JLNapo/BorneGEMI/Documents/Liste Composants.jpg

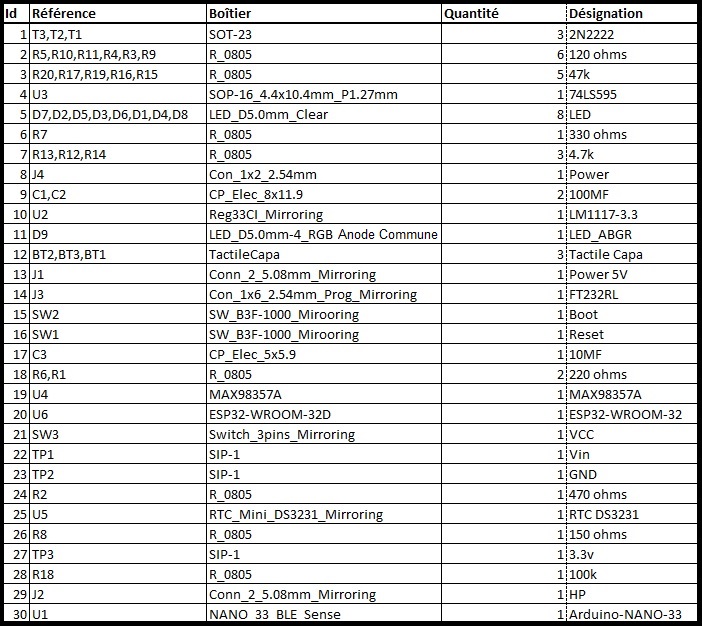
Documents/Liste Composants.jpg
