JLNapo/BorneGEMI/Documents/Plan Circuit.jpg

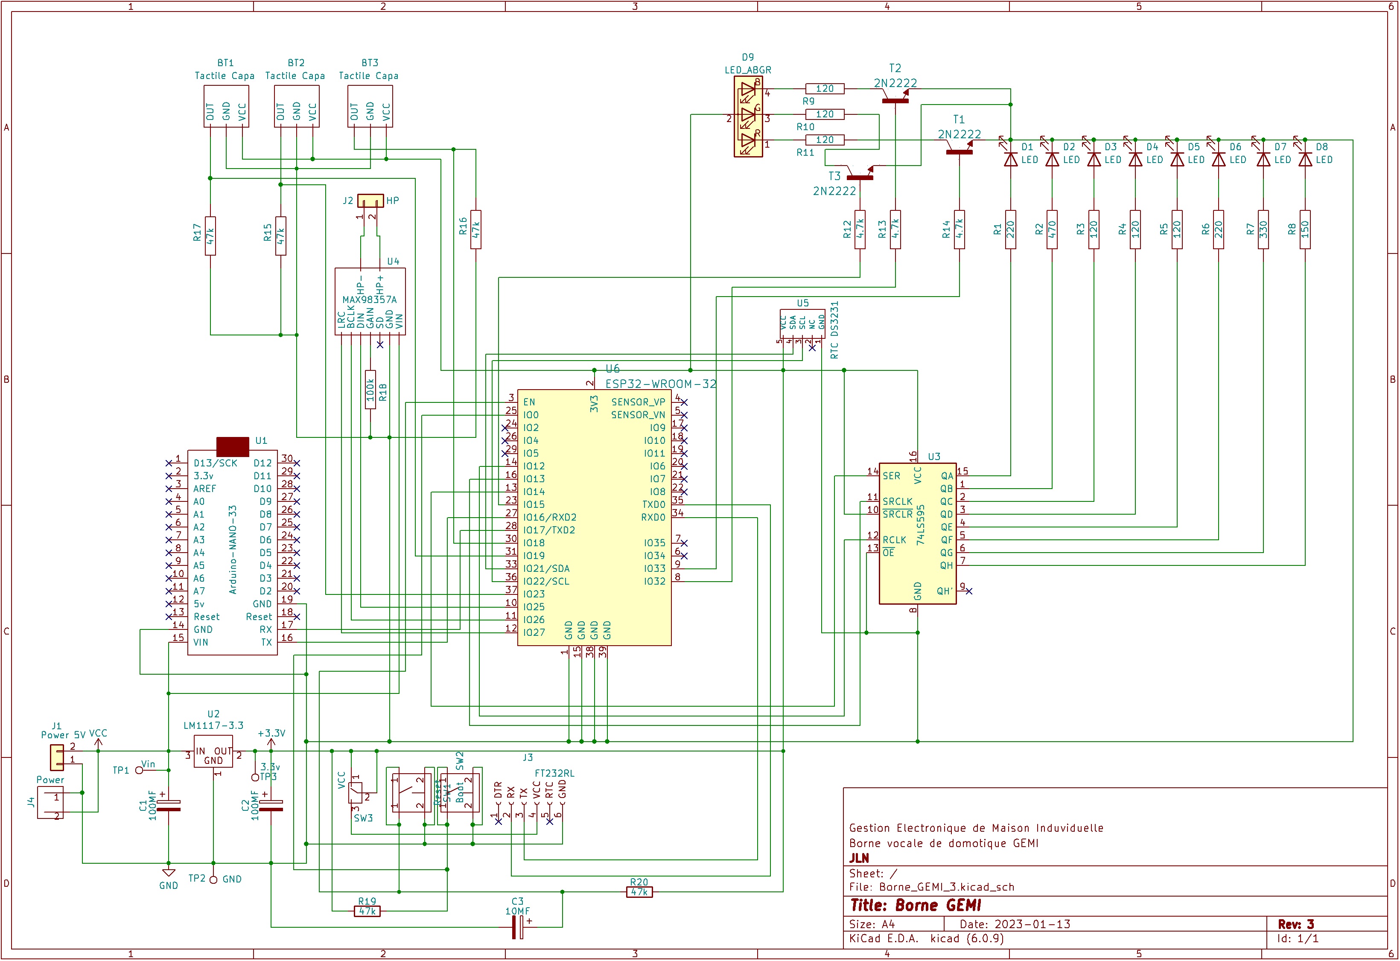
Documents/Plan Circuit.jpg
