JLNapo/BorneGEMI/Images/2N2222A_SMD.jpg

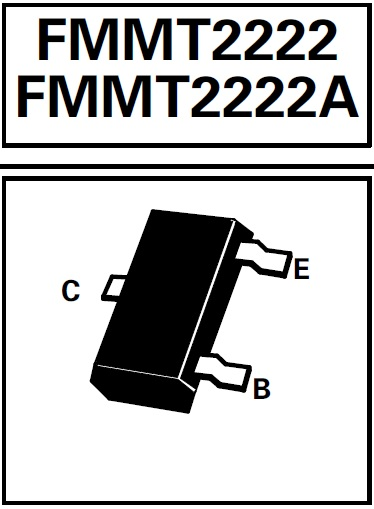
Images/2N2222A_SMD.jpg
