JLNapo/BorneGEMI/Images/74HC595-02.png

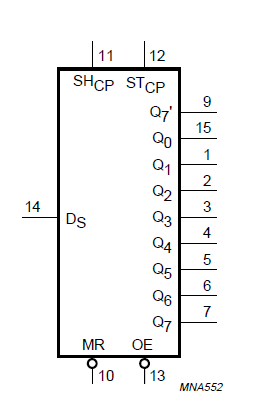
Images/74HC595-02.png
