JLNapo/BorneGEMI/Images/Alim-Diamètres.png

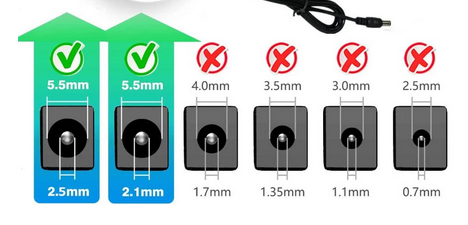
Images/Alim-Diamètres.png
