JLNapo/BorneGEMI/Images/BorneDessus.png

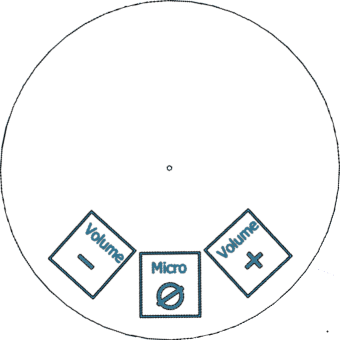
Images/BorneDessus.png
