JLNapo/BorneGEMI/Images/BorneDessusDouble.png

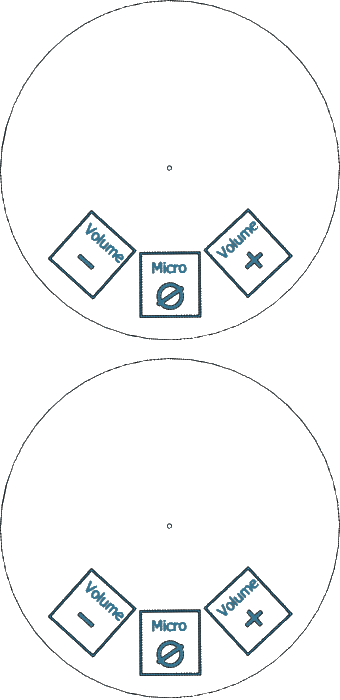
Images/BorneDessusDouble.png
