JLNapo/BorneGEMI/Images/Circuit Imprimé.jpg

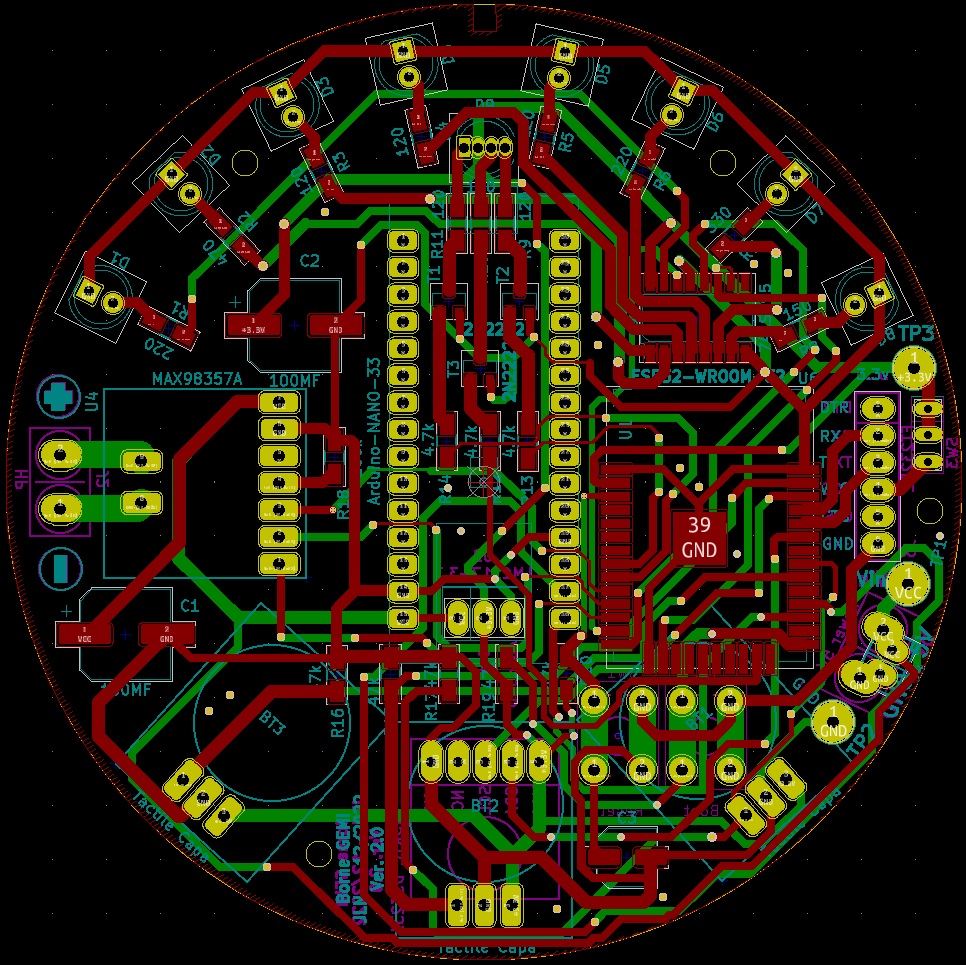
Images/Circuit Imprimé.jpg
