JLNapo/BorneGEMI/Images/DS3231.jpg

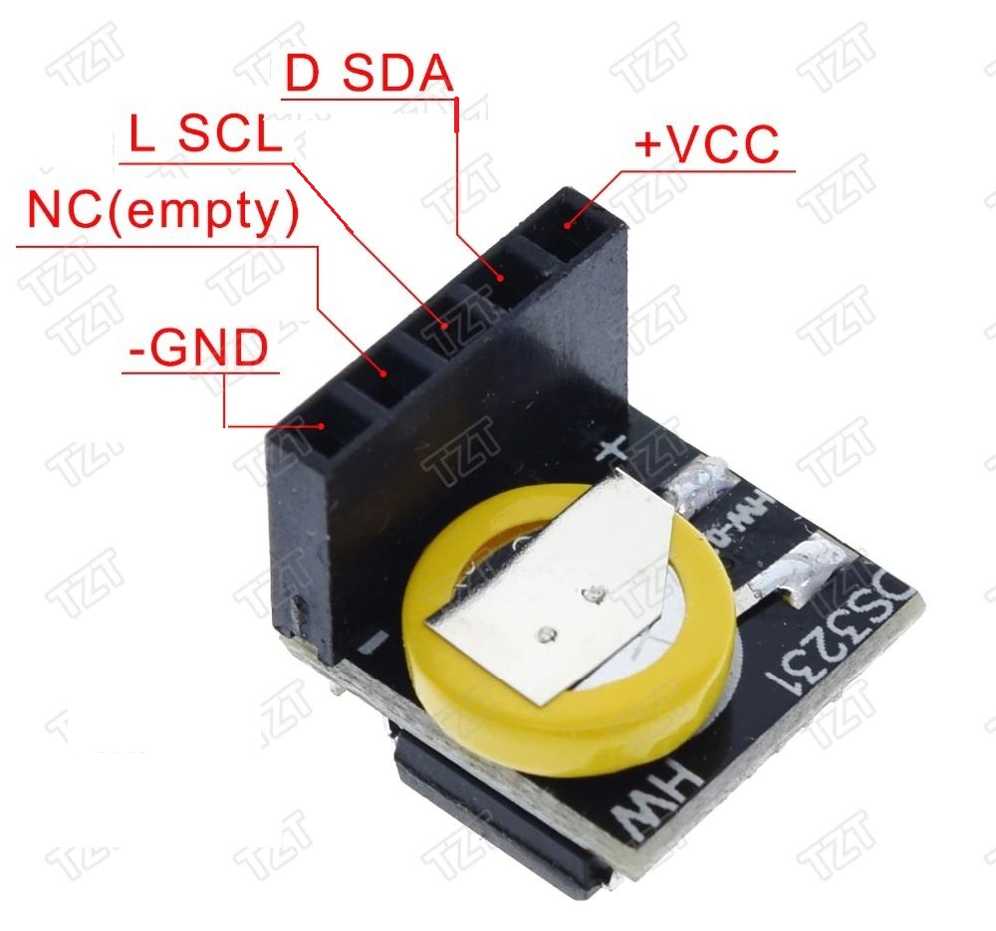
Images/DS3231.jpg
