JLNapo/BorneGEMI/Images/HTTM Dimensions.png

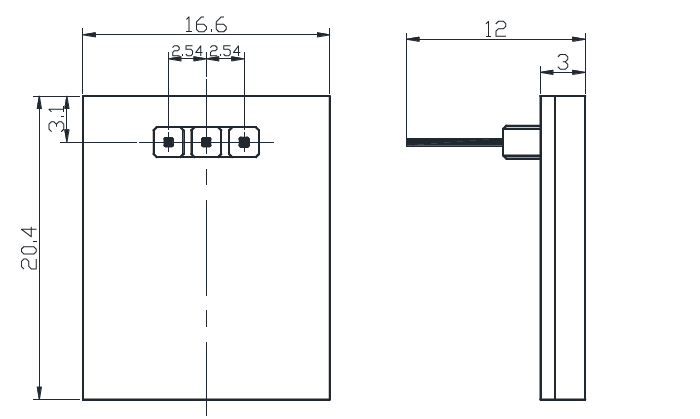
Images/HTTM Dimensions.png
