JLNapo/BorneGEMI/Images/img01.jpg

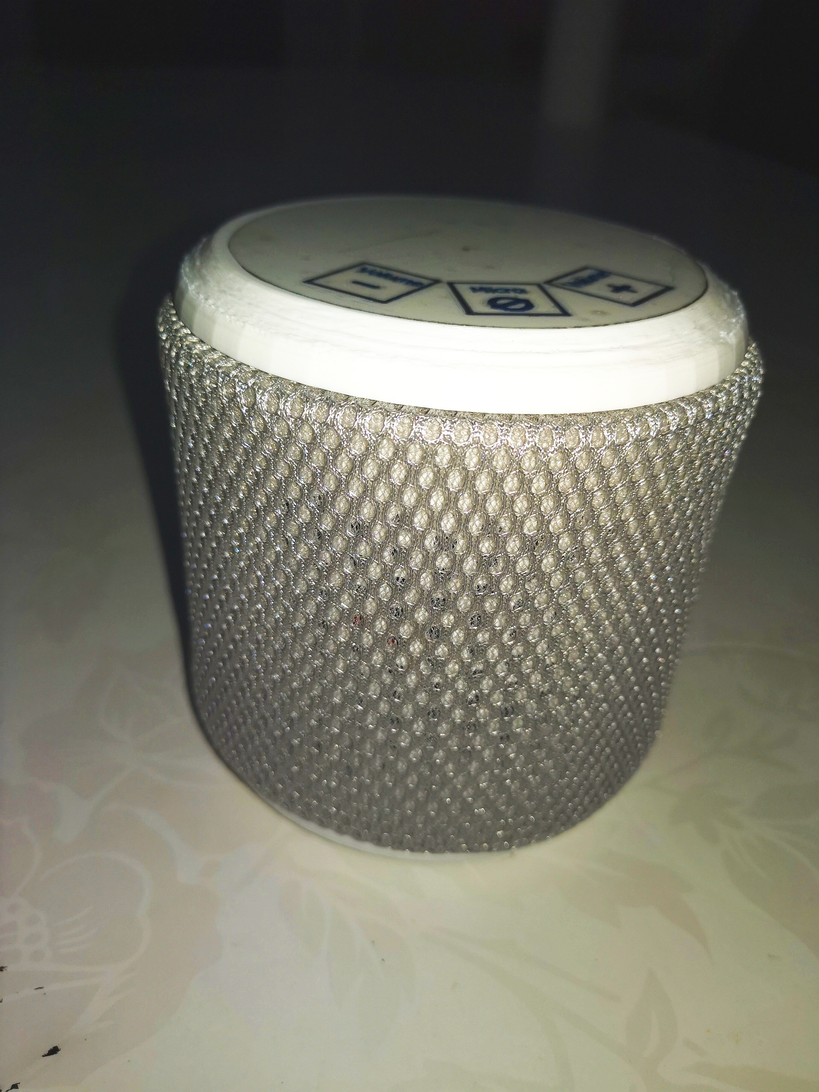
Images/img01.jpg
