JLNapo/BorneGEMI/Images/img02.jpg

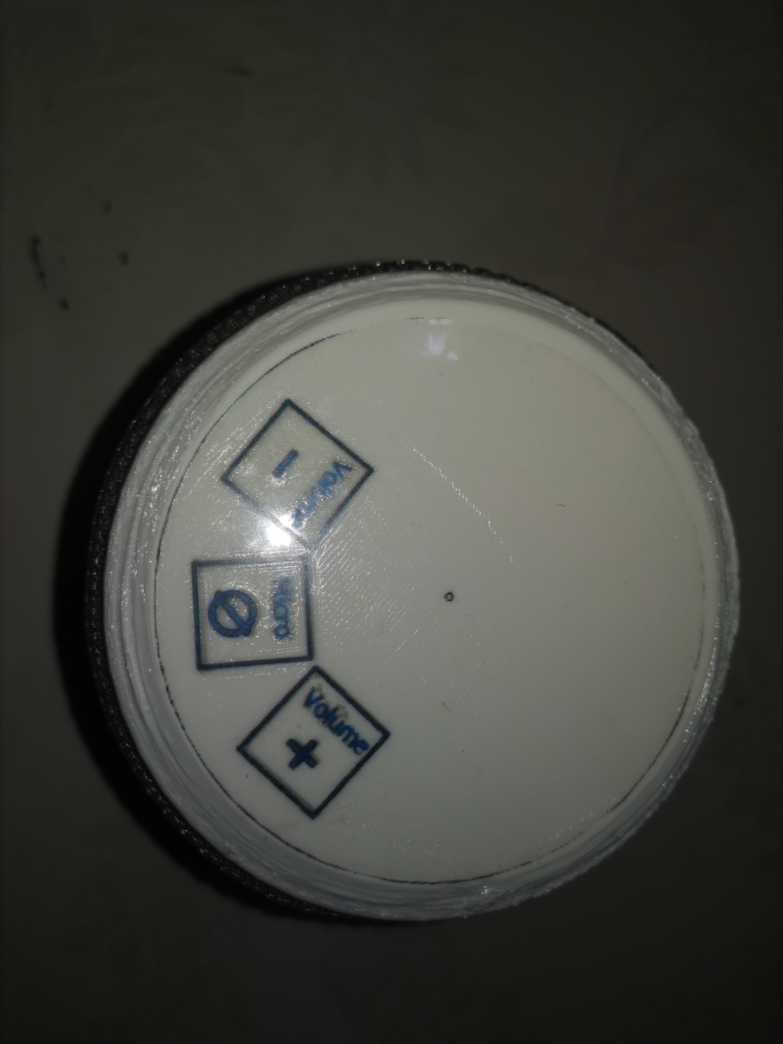
Images/img02.jpg
