JLNapo/BorneGEMI/Images/img03.jpg

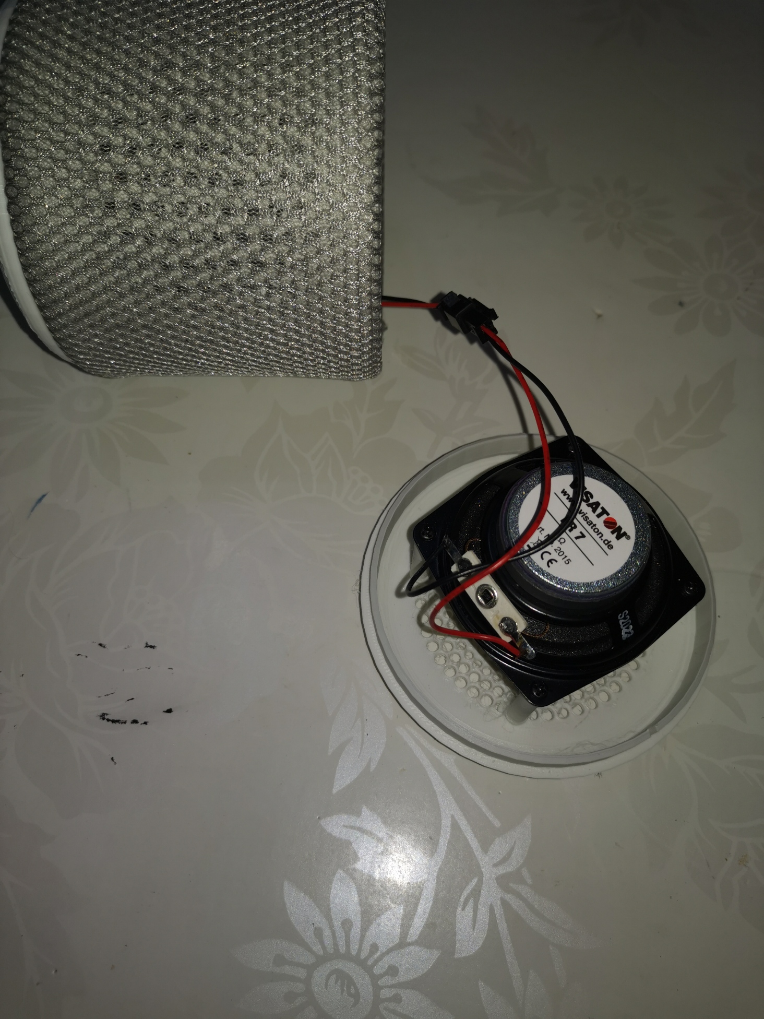
Images/img03.jpg
