JLNapo/BorneGEMI/Images/img04.jpg

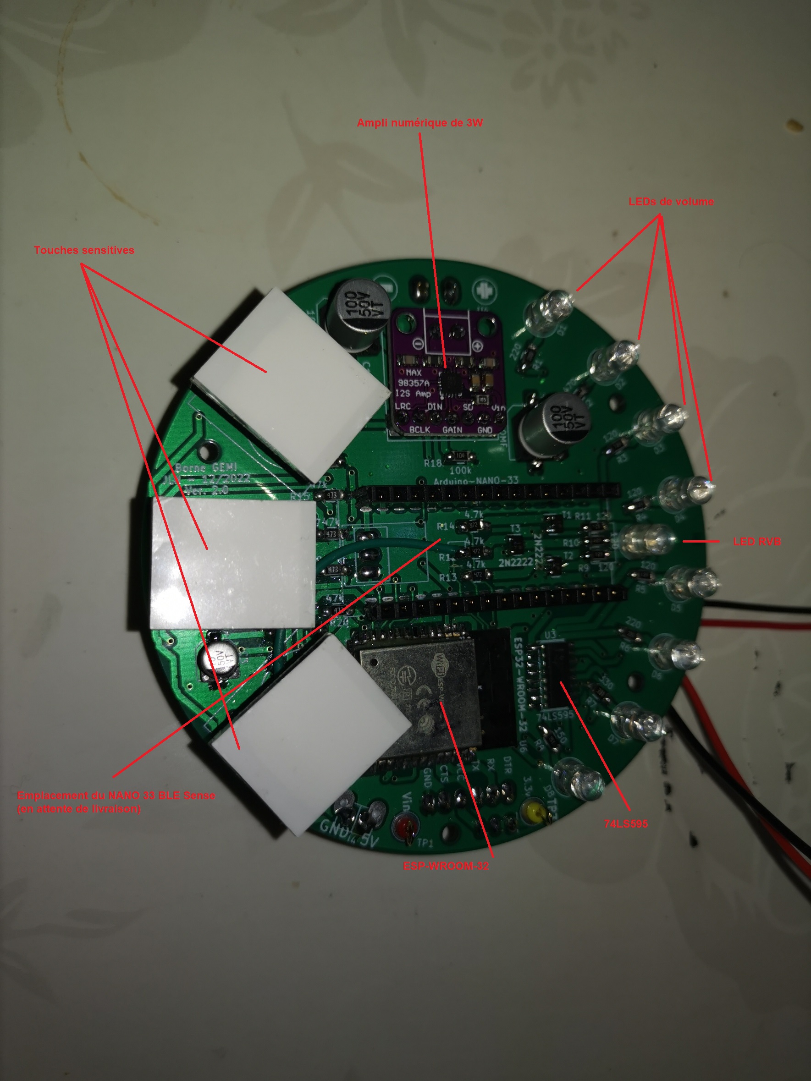
Images/img04.jpg
