JLNapo/BorneGEMI/Images/img05.jpg

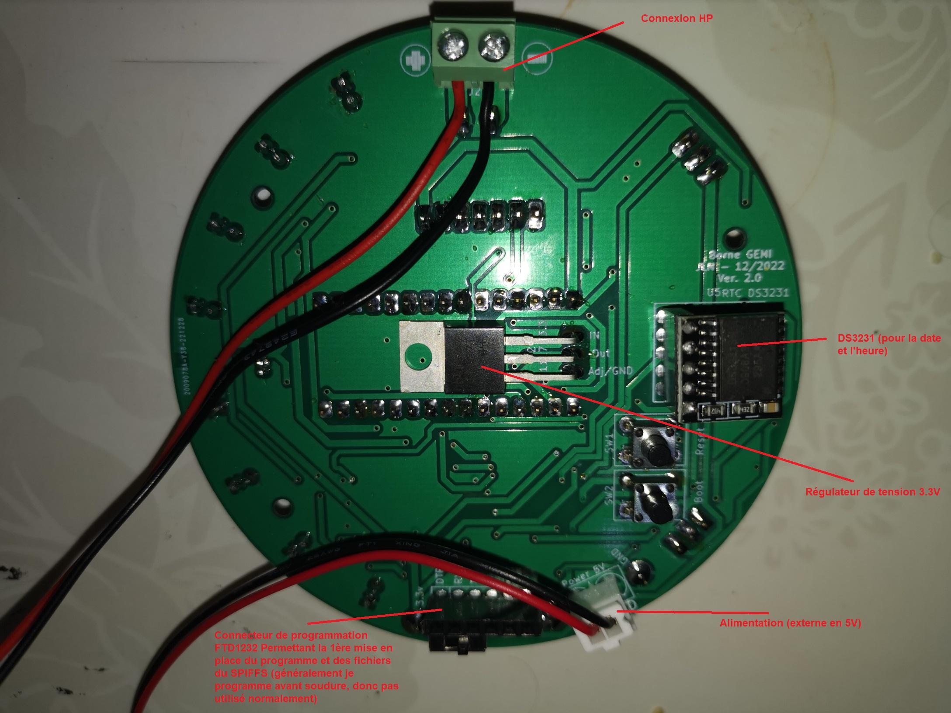
Images/img05.jpg
