JLNapo/BorneGEMI/Images/MAX98357A.jpg

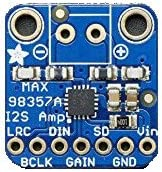
Images/MAX98357A.jpg
