JLNapo/BorneGEMI/Images/RGB_Anode_Commune.jpg

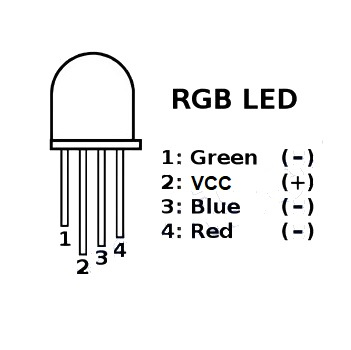
Images/RGB_Anode_Commune.jpg
