JLNapo/BorneGEMI/Images/TactileCapa.png

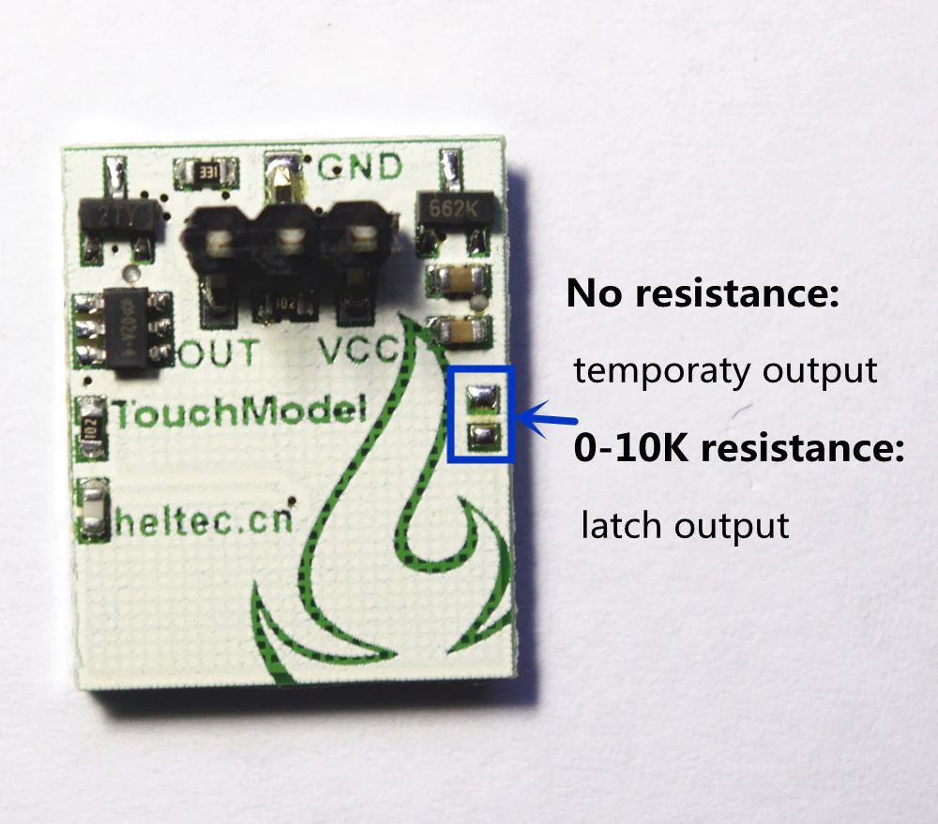
Images/TactileCapa.png
