JLNapo/BorneGEMI/Programmes/BorneGEMI_Nano_Salon/params.h

/*
  Copyright 2020-2021 Picovoice Inc.

  You may not use this file except in compliance with the license. A copy of the license is located in the "LICENSE"
  file accompanying this source.

  Unless required by applicable law or agreed to in writing, software distributed under the License is distributed on
  an "AS IS" BASIS, WITHOUT WARRANTIES OR CONDITIONS OF ANY KIND, either express or implied. See the License for the
  specific language governing permissions and limitations under the License.

  Nota: C'est ici qu'il faut placer les données compilées que vous avez créé et fournies par Picovoice.
*/

#include <stdint.h>

// Wake-word = hé gémi
static const uint8_t KEYWORD_ARRAY[480] __attribute__ ((aligned (16))) = {
  0x.., 0x.., 0x.., 0x.., 0x.., 0x.., 0x.., 0x.., 0x.., 0x.., 0x.., 0x.., 0x.., 0x.., 0x.., 0x.., 0x.., 0x..,
  0x.., 0x.., 0x.., 0x.., 0x.., 0x.., 0x.., 0x.., 0x.., 0x.., 0x.., 0x.., 0x.., 0x.., 0x.., 0x.., 0x.., 0x..,
  0x.., 0x.., 0x.., 0x.., 0x.., 0x.., 0x.., 0x.., 0x.., 0x.., 0x.., 0x.., 0x.., 0x.., 0x.., 0x.., 0x.., 0x..,
  0x.., 0x.., 0x.., 0x.., 0x.., 0x.., 0x.., 0x.., 0x.., 0x.., 0x.., 0x.., 0x.., 0x.., 0x.., 0x.., 0x.., 0x..,
  0x.., 0x.., 0x.., 0x.., 0x.., 0x.., 0x.., 0x.., 0x.., 0x.., 0x.., 0x.., 0x.., 0x.., 0x.., 0x.., 0x.., 0x..,
  0x.., 0x.., 0x.., 0x.., 0x.., 0x.., 0x.., 0x.., 0x.., 0x.., 0x.., 0x.., 0x.., 0x.., 0x.., 0x.., 0x.., 0x..,
  .............
  0x.., 0x.., 0x.., 0x.., 0x.., 0x.., 0x.., 0x.., 0x.., 0x.., 0x.., 0x.., 0x.., 0x.., 0x.., 0x.., 0x.., 0x..,
  0x.., 0x.., 0x.., 0x.., 0x.., 0x.., 0x.., 0x.., 0x.., 0x.., 0x.., 0x.., 0x.., 0x.., 0x.., 0x.., 0x.., 0x..,
  0x.., 0x.., 0x.., 0x.., 0x.., 0x.., 0x.., 0x.., 0x.., 0x.., 0x.., 0x.., 0x.., 0x.., 0x.., 0x.., 0x.., 0x..,
  0x.., 0x.., 0x.., 0x.., 0x.., 0x.., 0x.., 0x.., 0x.., 0x.., 0x.., 0x.., 0x.., 0x.., 0x.., 0x.., 0x.., 0x..,
};

// context des commandes
static const uint8_t CONTEXT_ARRAY[] = {
  0x.., 0x.., 0x.., 0x.., 0x.., 0x.., 0x.., 0x.., 0x.., 0x.., 0x.., 0x.., 0x.., 0x.., 0x.., 0x.., 0x.., 0x..,
  0x.., 0x.., 0x.., 0x.., 0x.., 0x.., 0x.., 0x.., 0x.., 0x.., 0x.., 0x.., 0x.., 0x.., 0x.., 0x.., 0x.., 0x..,
  0x.., 0x.., 0x.., 0x.., 0x.., 0x.., 0x.., 0x.., 0x.., 0x.., 0x.., 0x.., 0x.., 0x.., 0x.., 0x.., 0x.., 0x..,
  0x.., 0x.., 0x.., 0x.., 0x.., 0x.., 0x.., 0x.., 0x.., 0x.., 0x.., 0x.., 0x.., 0x.., 0x.., 0x.., 0x.., 0x..,
  0x.., 0x.., 0x.., 0x.., 0x.., 0x.., 0x.., 0x.., 0x.., 0x.., 0x.., 0x.., 0x.., 0x.., 0x.., 0x.., 0x.., 0x..,
  0x.., 0x.., 0x.., 0x.., 0x.., 0x.., 0x.., 0x.., 0x.., 0x.., 0x.., 0x.., 0x.., 0x.., 0x.., 0x.., 0x.., 0x..,
  .............
  0x.., 0x.., 0x.., 0x.., 0x.., 0x.., 0x.., 0x.., 0x.., 0x.., 0x.., 0x.., 0x.., 0x.., 0x.., 0x.., 0x.., 0x..,
  0x.., 0x.., 0x.., 0x.., 0x.., 0x.., 0x.., 0x.., 0x.., 0x.., 0x.., 0x.., 0x.., 0x.., 0x.., 0x.., 0x.., 0x..,
  0x.., 0x.., 0x.., 0x.., 0x.., 0x.., 0x.., 0x.., 0x.., 0x.., 0x.., 0x.., 0x.., 0x.., 0x.., 0x.., 0x.., 0x..,
  0x.., 0x.., 0x.., 0x.., 0x.., 0x.., 0x.., 0x.., 0x.., 0x.., 0x.., 0x.., 0x.., 0x.., 0x.., 0x.., 0x.., 0x..,
};








/* END */
